haroldm/cantoto/firmware/src/system/ring.h

#ifndef __RING_H__
#define __RING_H__

#include <inttypes.h>

typedef int32_t ring_size_t;

struct ring_t {
  uint8_t *data;
  ring_size_t size;
  volatile uint32_t begin;
  volatile uint32_t end;
  uint32_t overflow;
};

void ring_init(struct ring_t *ring, uint8_t *buf, ring_size_t size);
int32_t ring_write_ch(struct ring_t *ring, uint8_t ch);
int32_t ring_write(struct ring_t *ring, uint8_t *data, ring_size_t size);
uint8_t ring_read_ch(struct ring_t *ring, uint8_t *ch);
uint32_t ring_get_overflow(struct ring_t *ring);

#endif // __RING_H__
